iMike78/nest-mini-drop-in-pcb/pics/3D.png

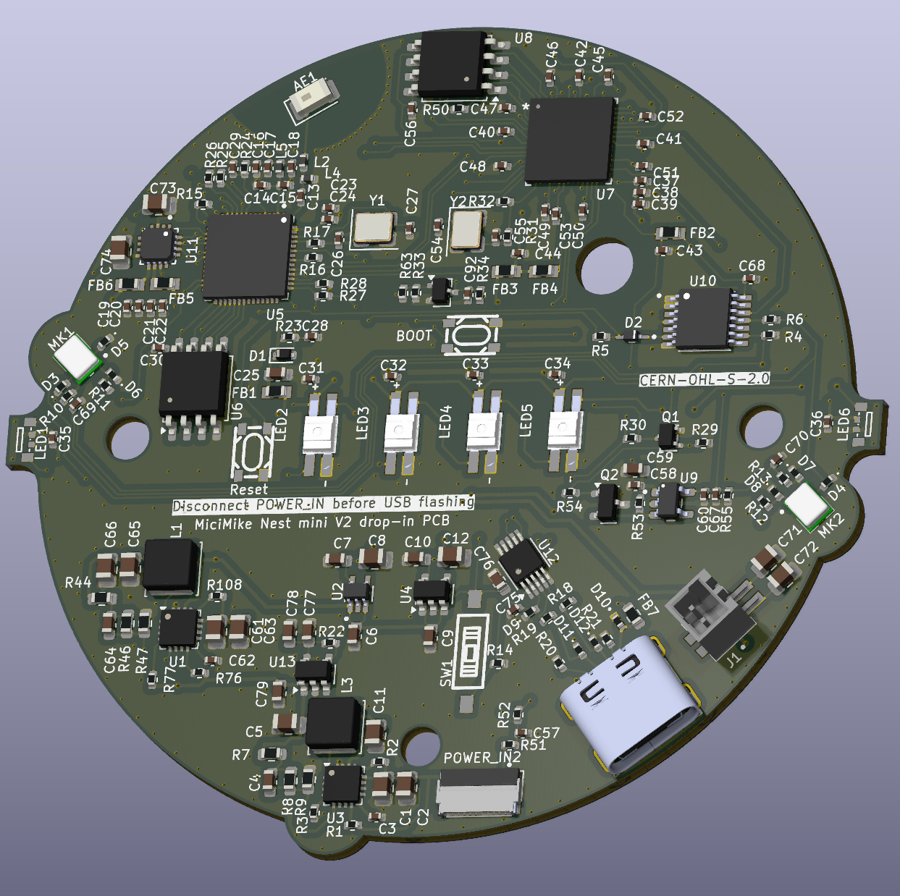
pics/3D.png
