iMike78/nest-mini-drop-in-pcb/pics/In1_Cu.png

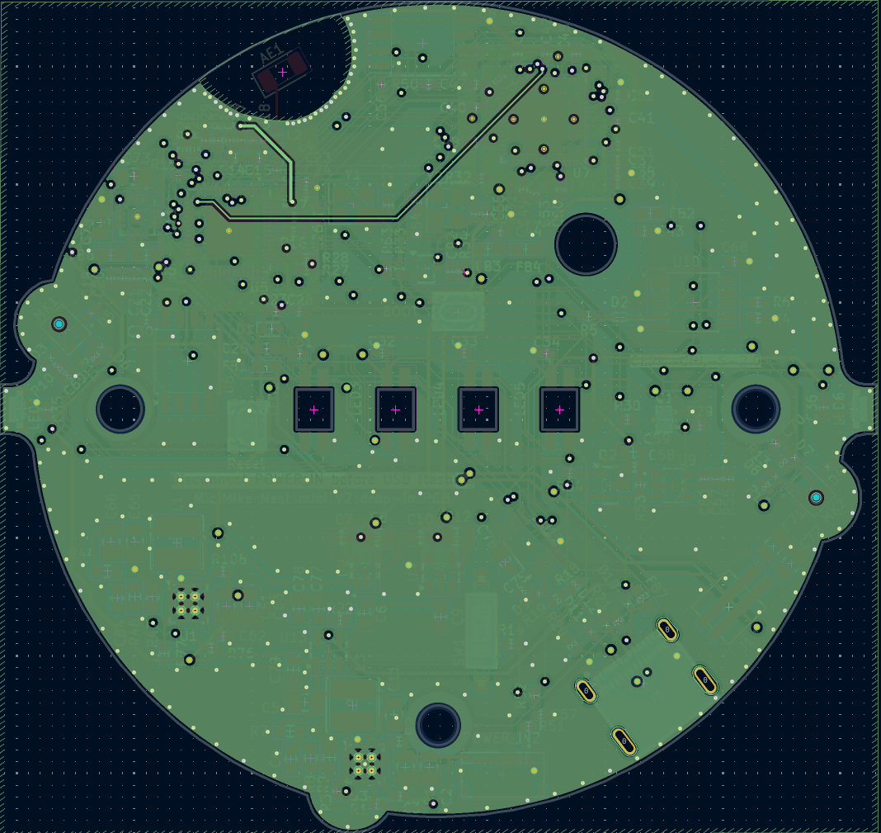
pics/In1_Cu.png
