iMike78/nest-mini-drop-in-pcb/pics/MiciMike_Nest__PCB_Prototype_2.png

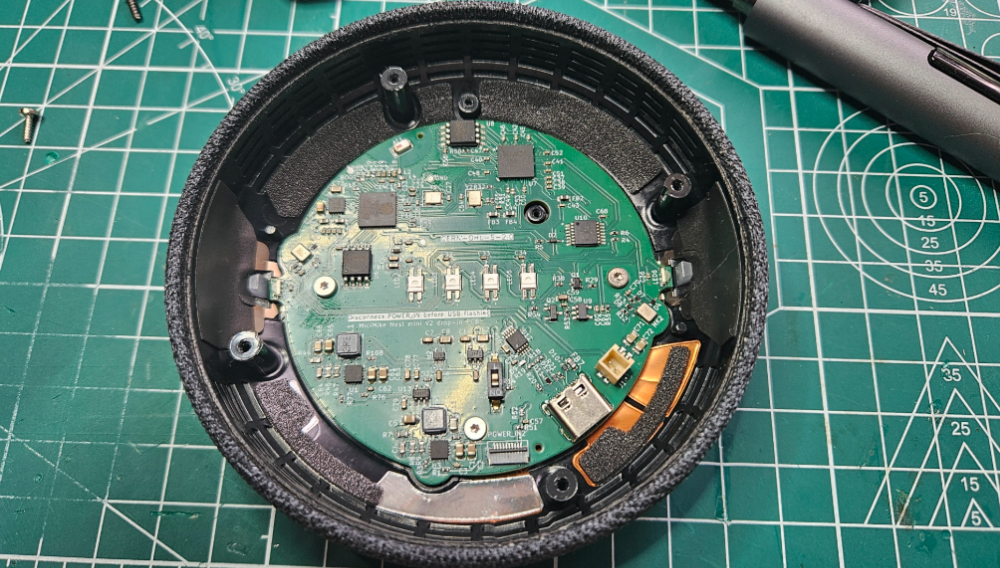
pics/MiciMike_Nest__PCB_Prototype_2.png
