iMike78/nest-mini-drop-in-pcb/parts/QFN_F60B-C24_XMO.step

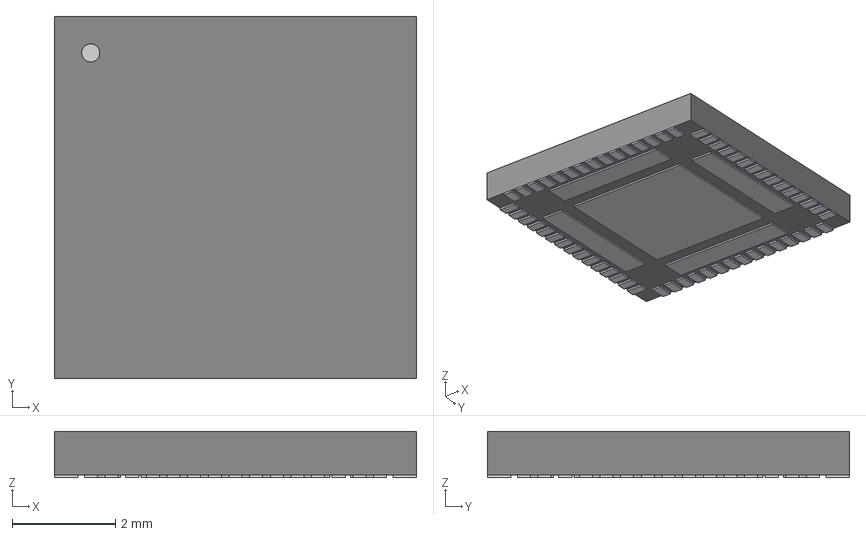
[picture p27: CAD file, 2025-07-18]
parts/QFN_F60B-C24_XMO.step
7.01 x 7.01 x 0.892 mm
