iMike78/nest-mini-drop-in-pcb/parts/OBJ_SW-SMD_2P-L6.2-W2.5-LS9.4.obj

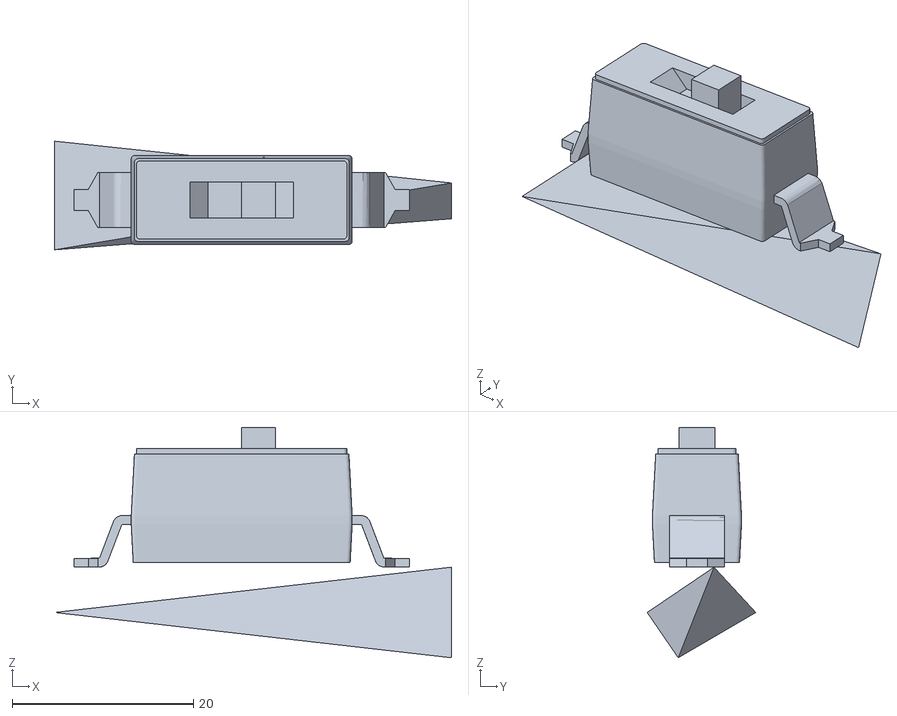
[picture p28: CAD file, 2025-06-25]
parts/OBJ_SW-SMD_2P-L6.2-W2.5-LS9.4.obj
43.8 x 12.0 x 25.5
