iMike78/nest-mini-drop-in-pcb/parts/SW-SMD_2P-L6.2-W2.5-LS9.4.dxf

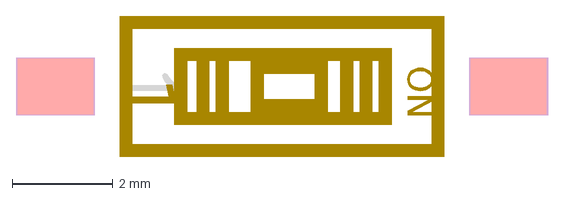
[picture p29: CAD file, 2025-06-25]
parts/SW-SMD_2P-L6.2-W2.5-LS9.4.dxf
ON
1
