iMike78/nest-mini-drop-in-pcb/parts/USB-C-SMD_TYPE-C-USB-18_2025-06-23.dxf

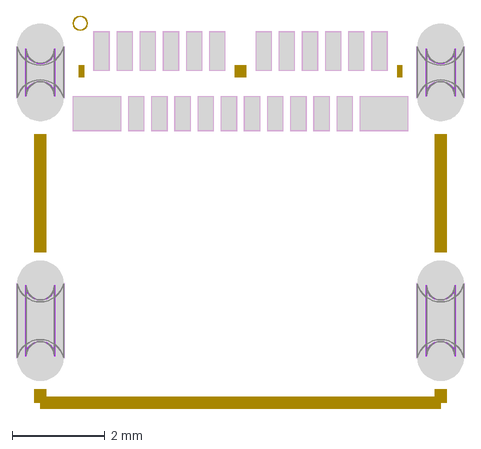
[picture p30: CAD file, 2025-06-24]
parts/USB-C-SMD_TYPE-C-USB-18_2025-06-23.dxf
9.69 x 8.47 mm
